Paulina99Z/documentacion-proyecto/img/maqueta 1-5/prototipo 1/135px-Propuesta1MaquetaNataliaSotoPaulinaZuñiga12022TDI4.jpeg

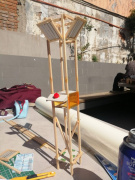
img/maqueta 1-5/prototipo 1/135px-Propuesta1MaquetaNataliaSotoPaulinaZuñiga12022TDI4.jpeg
