Paulina99Z/documentacion-proyecto/img/maqueta 1-5/prototipo 1/Propuesta1MaquetaNataliaSotoPaulinaZuñiga12022TDI3.jpeg

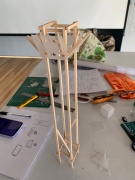
img/maqueta 1-5/prototipo 1/Propuesta1MaquetaNataliaSotoPaulinaZuñiga12022TDI3.jpeg
