Paulina99Z/documentacion-proyecto/img/maqueta 1-5/prototipo 2/135px-Modelototemprototipo2nataliasotopaulinazuñigatix20223.jpeg

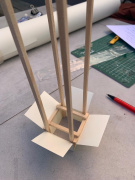
img/maqueta 1-5/prototipo 2/135px-Modelototemprototipo2nataliasotopaulinazuñigatix20223.jpeg
