Paulina99Z/documentacion-proyecto/img/maqueta 1-5/prototipo 2/Modelototemprototipo2nataliasotopaulinazuñigatix2022.jpeg

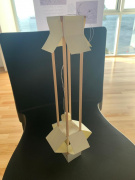
img/maqueta 1-5/prototipo 2/Modelototemprototipo2nataliasotopaulinazuñigatix2022.jpeg
