Paulina99Z/documentacion-proyecto/img/maqueta 1-5/prototipo 3/Propuesta3MaquetaNataliaSotoPaulinaZuñiga12022TDI1.jpeg

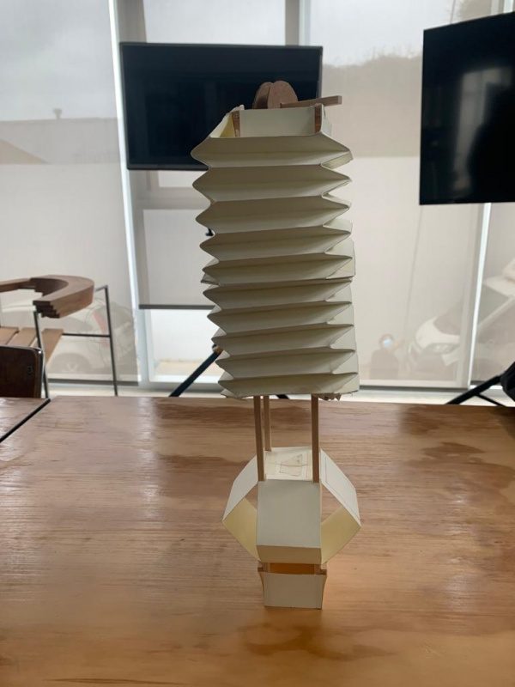
img/maqueta 1-5/prototipo 3/Propuesta3MaquetaNataliaSotoPaulinaZuñiga12022TDI1.jpeg
