Paulina99Z/documentacion-proyecto/img/totem 1-1/dibujo lineal totem.jpg

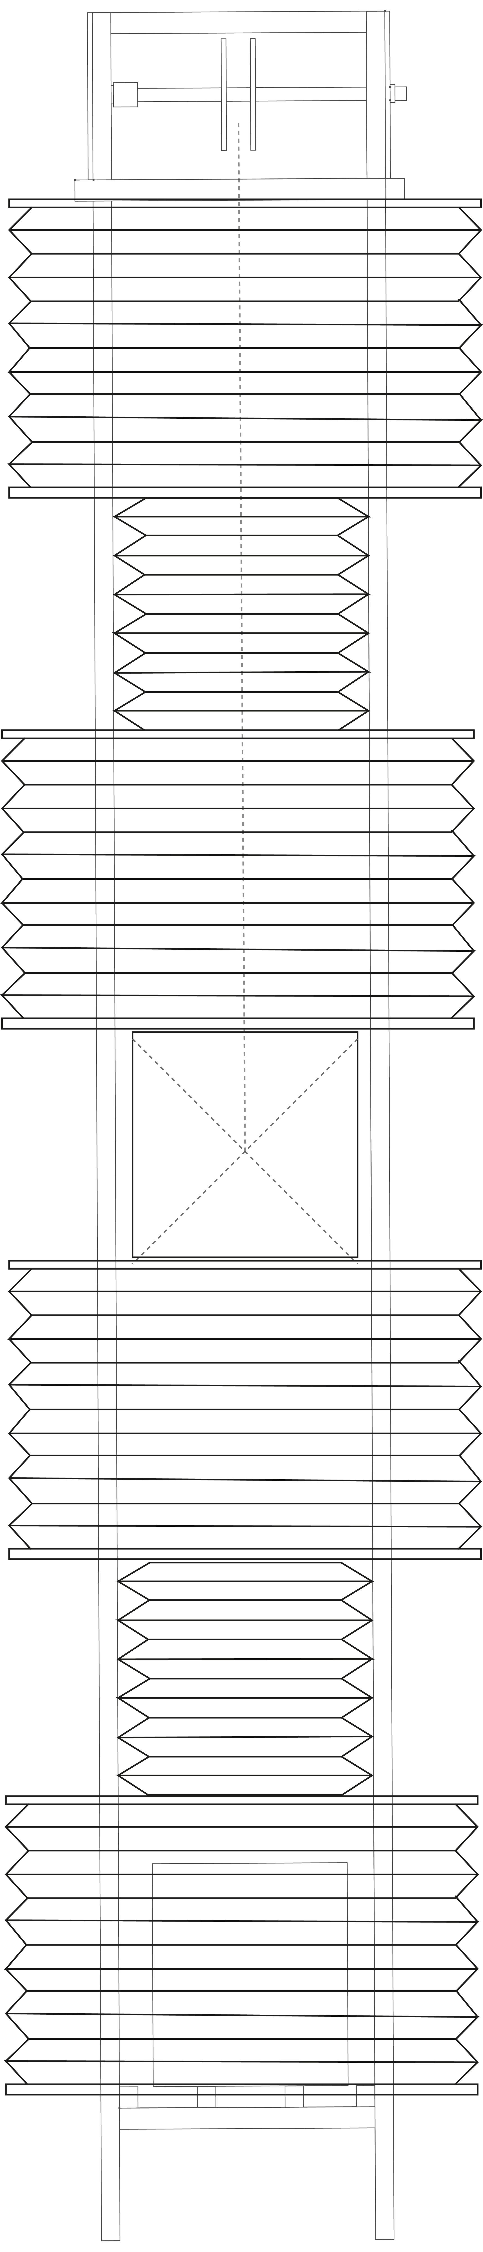
img/totem 1-1/dibujo lineal totem.jpg
