Paulina99Z/documentacion-proyecto/img/totem 1-1/Totem dibujos-02.png

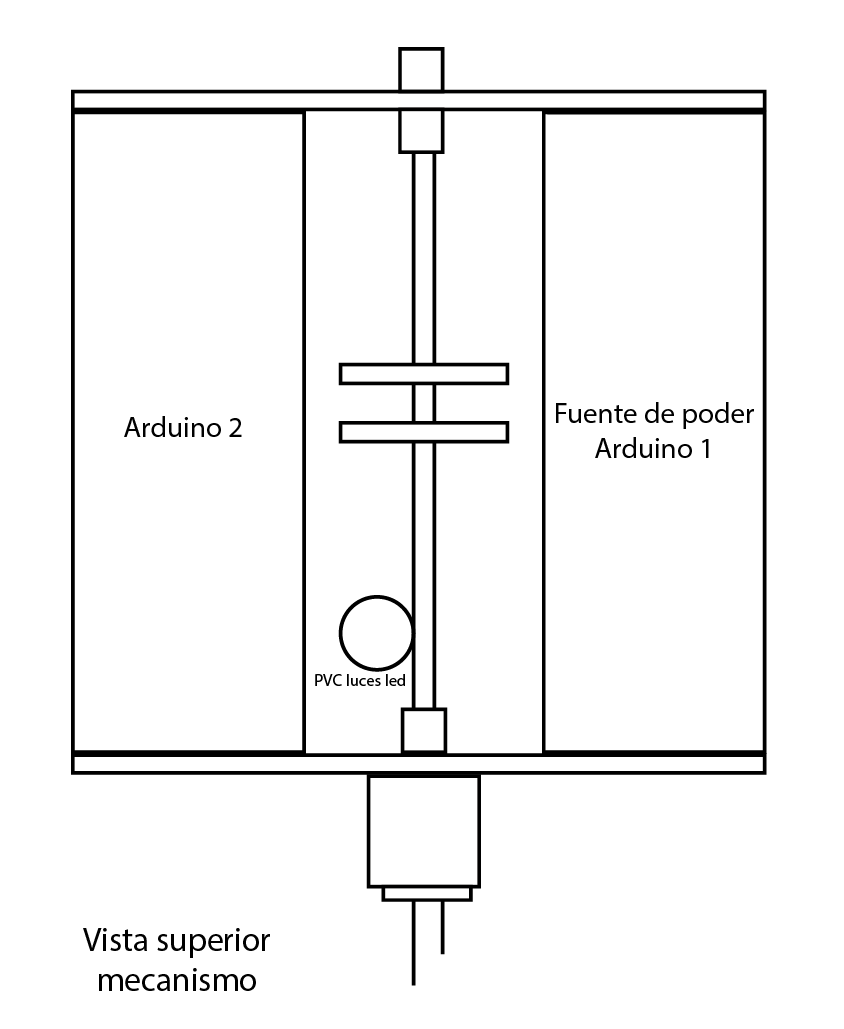
img/totem 1-1/Totem dibujos-02.png
