Paulina99Z/documentacion-proyecto/img/totem 1-1/WhatsApp Image 2022-05-18 at 11.18.49 PM.jpeg

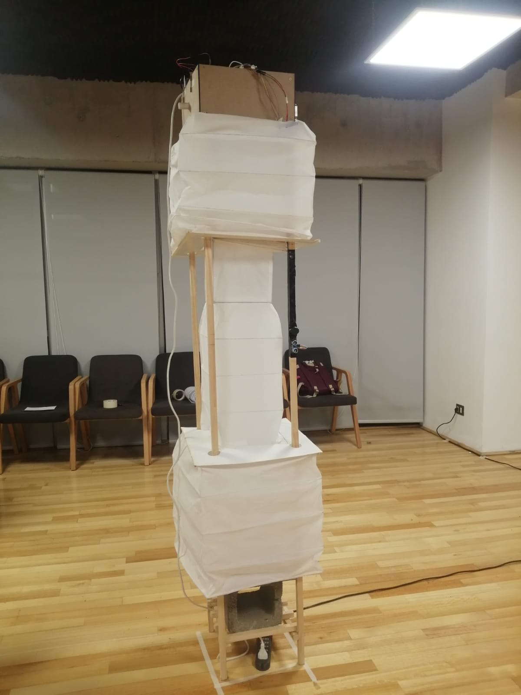
img/totem 1-1/WhatsApp Image 2022-05-18 at 11.18.49 PM.jpeg
