Paulina99Z/documentacion-proyecto/ino/codigo para motor s - joystick.png

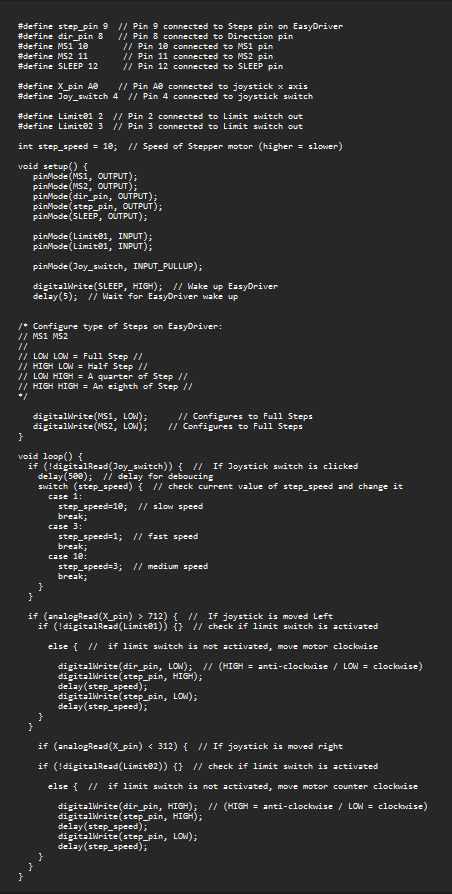
ino/codigo para motor s - joystick.png
