Paulina99Z/documentacion-proyecto/ino/codigo para sensor ultrasonico.png

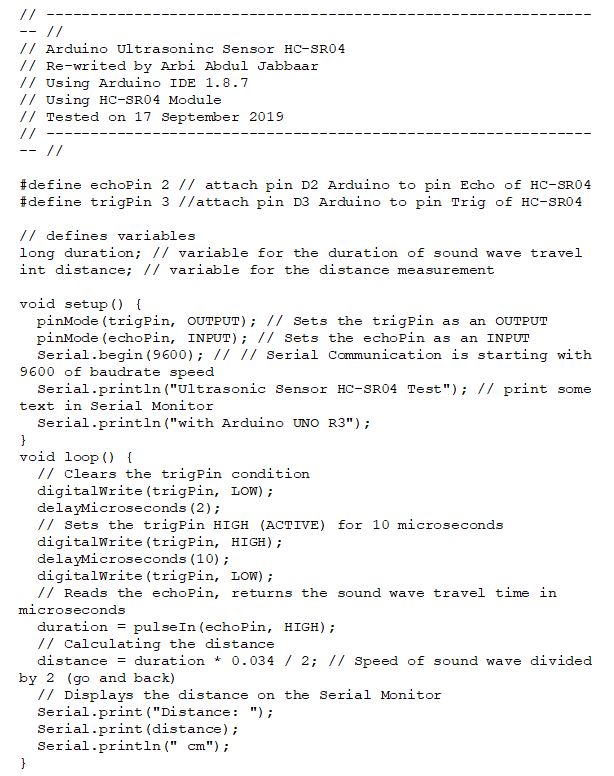
ino/codigo para sensor ultrasonico.png
