Paulina99Z/documentacion-proyecto/ino/conexion arduino y sensor ultrasonico.png

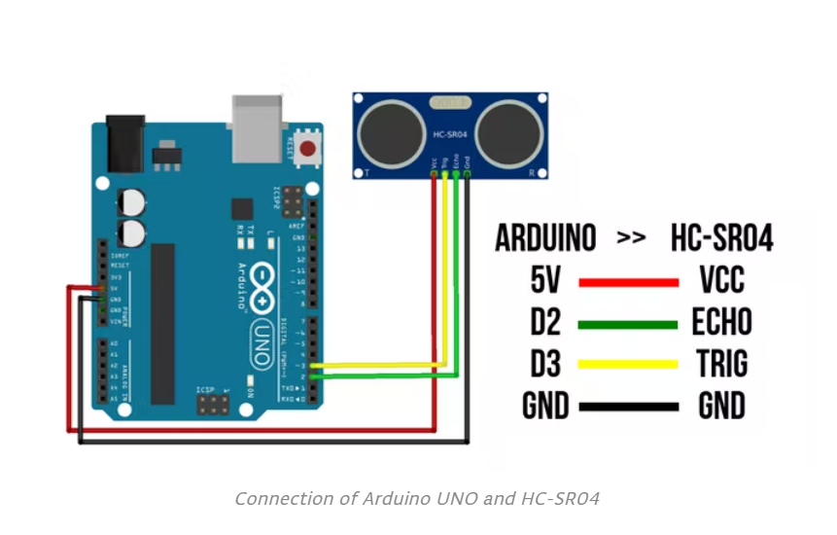
ino/conexion arduino y sensor ultrasonico.png
